inguardians/InG_Sparring_Boards/trunk/version_1_pi/images/InG_version1_pi_progression_back.JPG

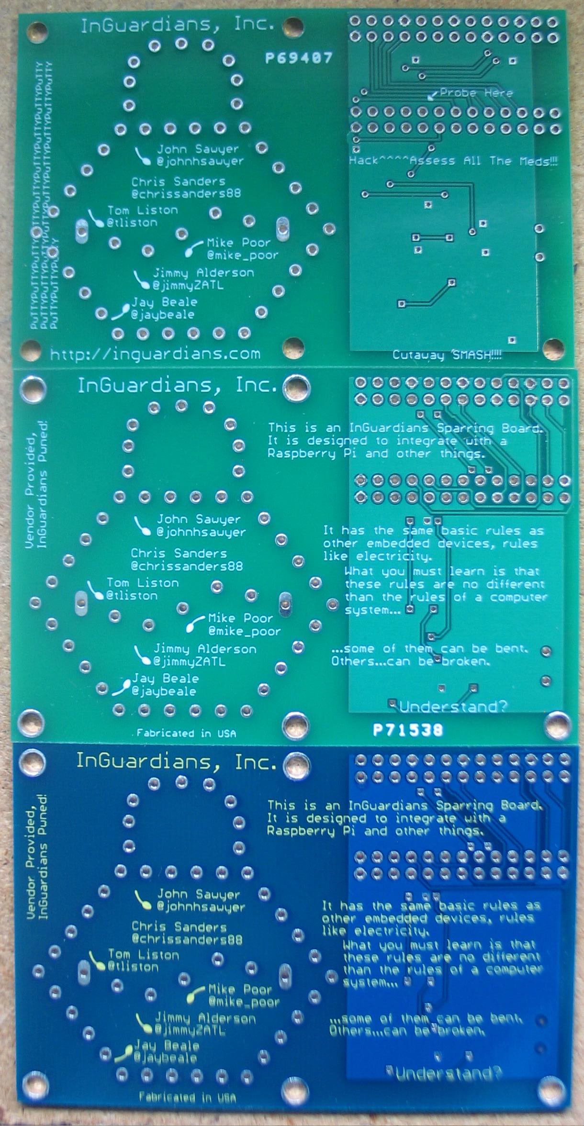
trunk/version_1_pi/images/InG_version1_pi_progression_back.JPG
