inguardians/InG_Sparring_Boards/trunk/version_1_pi/images/InG_version1_pi_led_testing_1.jpg

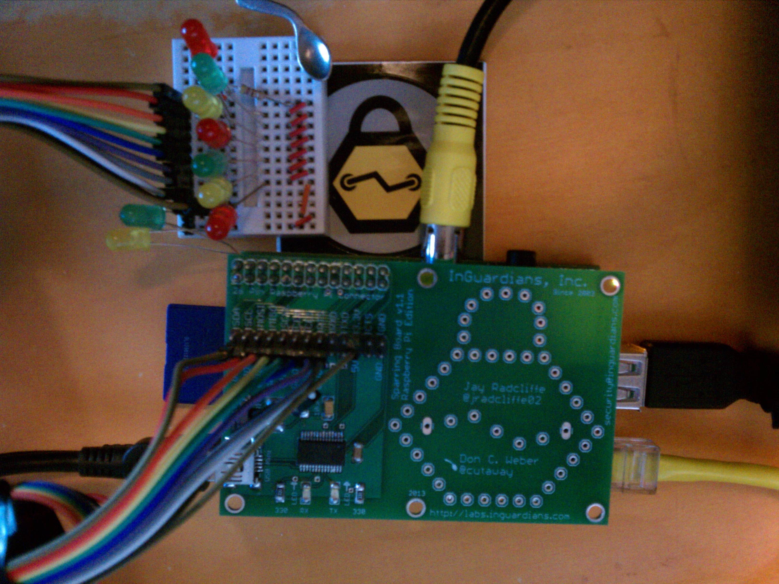
trunk/version_1_pi/images/InG_version1_pi_led_testing_1.jpg
